cariboulabs/cariboulite_hw/doc/s-params/hfcn_from_cm.png

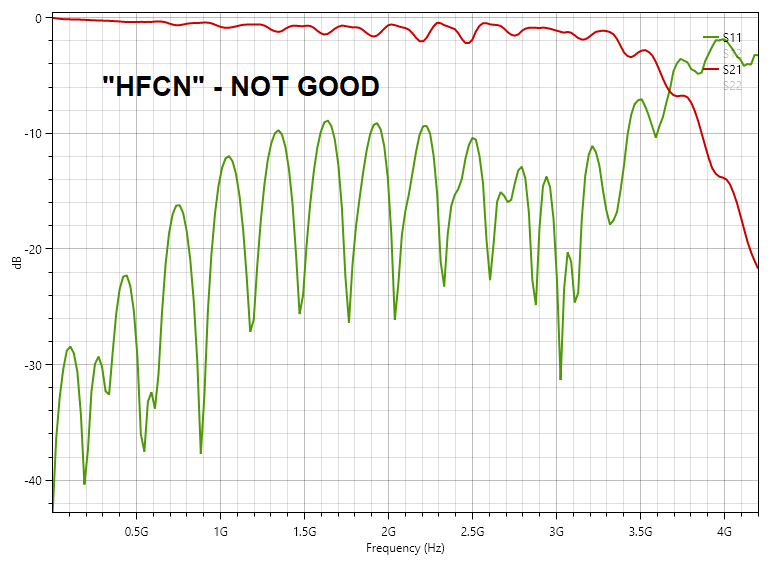
doc/s-params/hfcn_from_cm.png
