cariboulabs/cariboulite_hw/doc/s-params/hfcn_from_minicircuits.png

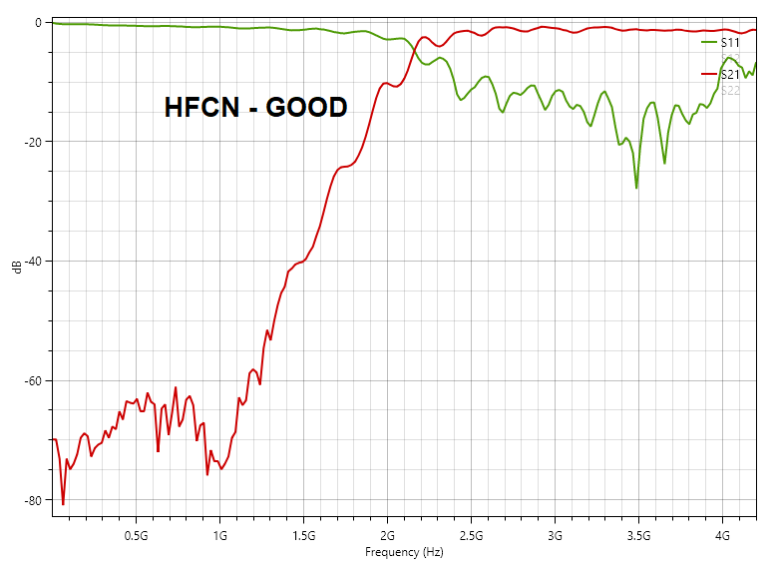
doc/s-params/hfcn_from_minicircuits.png
