cariboulabs/cariboulite_hw/doc/s-params/lineup.jpg

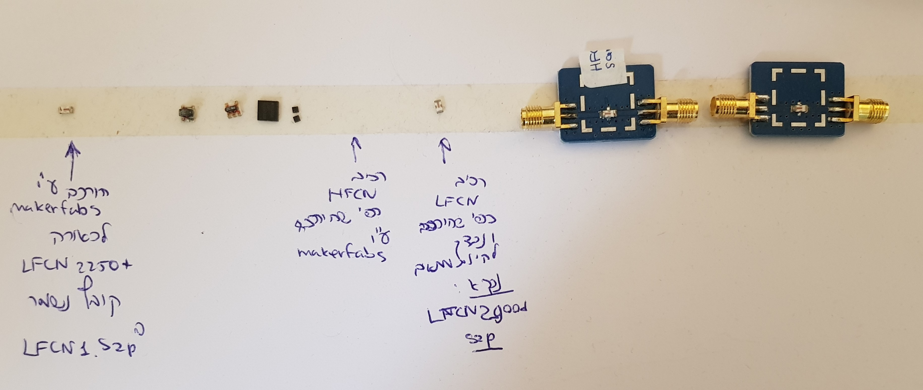
doc/s-params/lineup.jpg
