cariboulabs/cariboulite_hw/doc/screenshots/sdr_pp_fm_radio.png

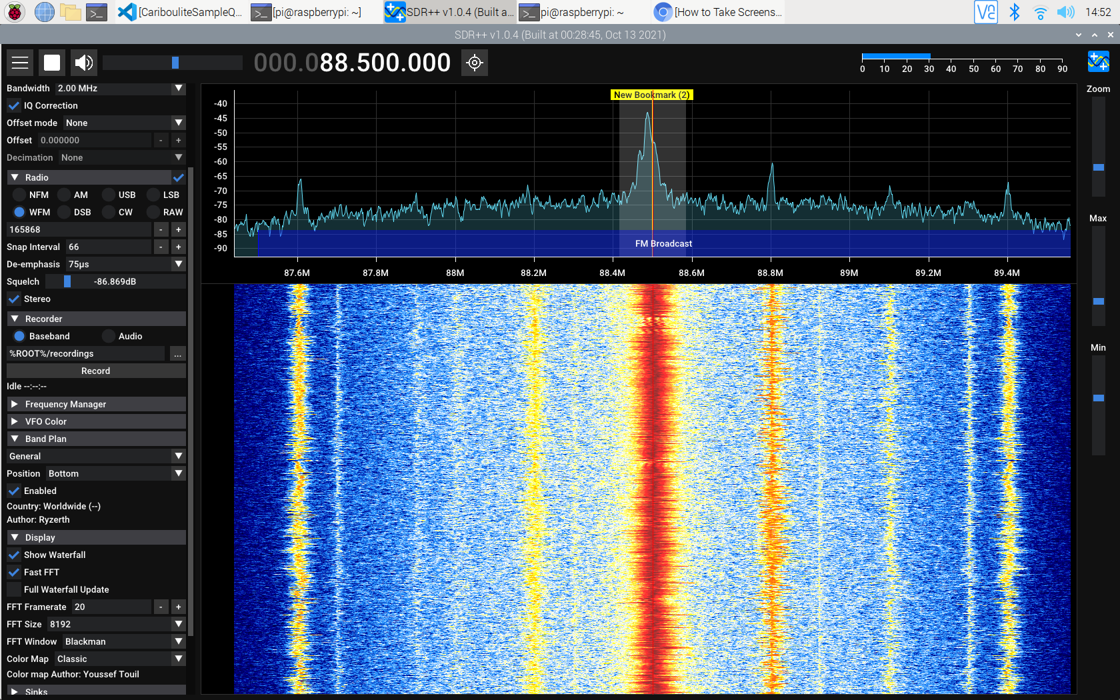
doc/screenshots/sdr_pp_fm_radio.png
