cariboulabs/cariboulite_hw/doc/screenshots/sdr_pp_ism.png

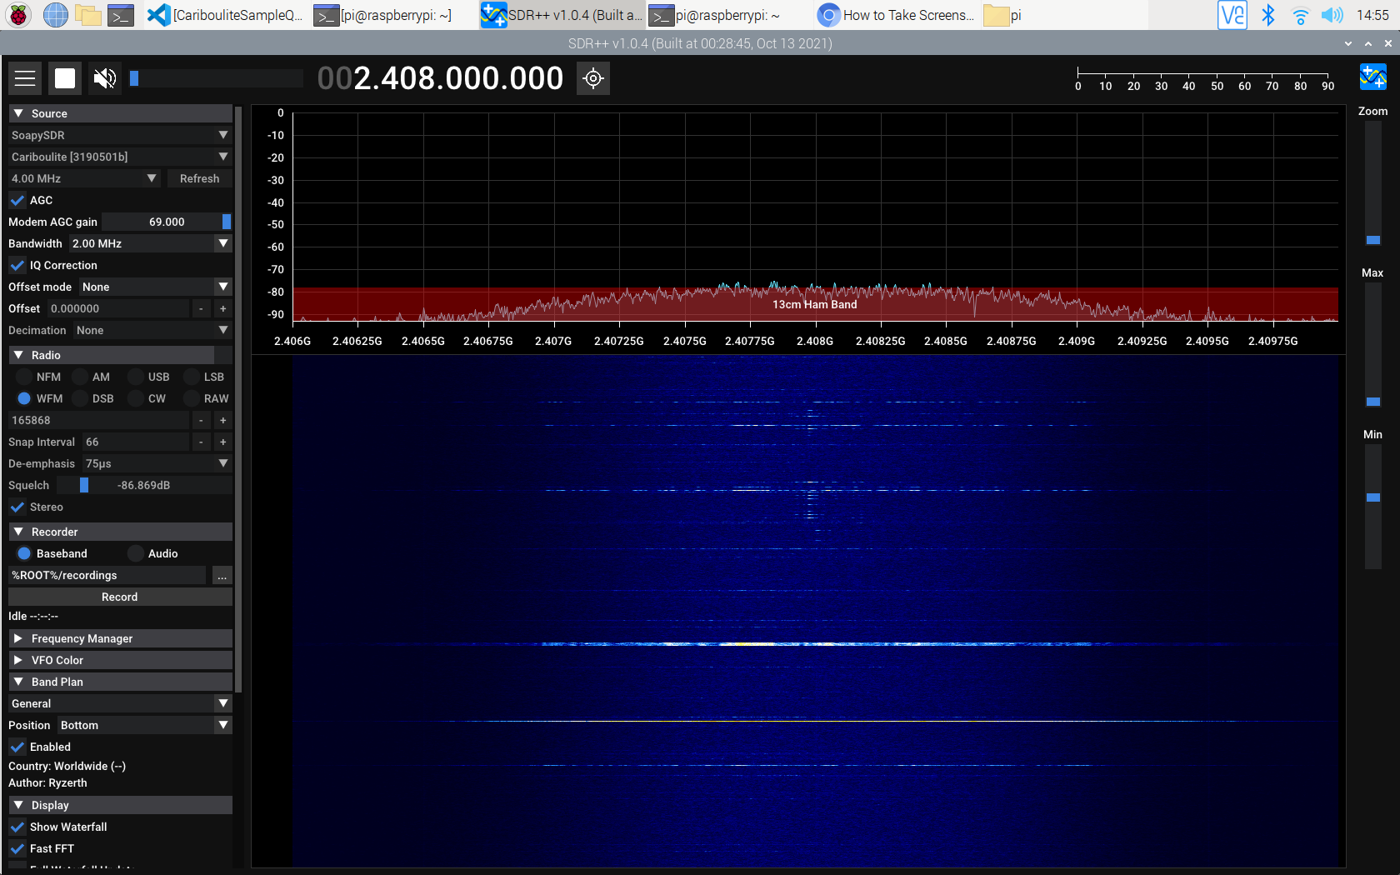
doc/screenshots/sdr_pp_ism.png
