cariboulabs/cariboulite_hw/doc/system/power_sketch.png

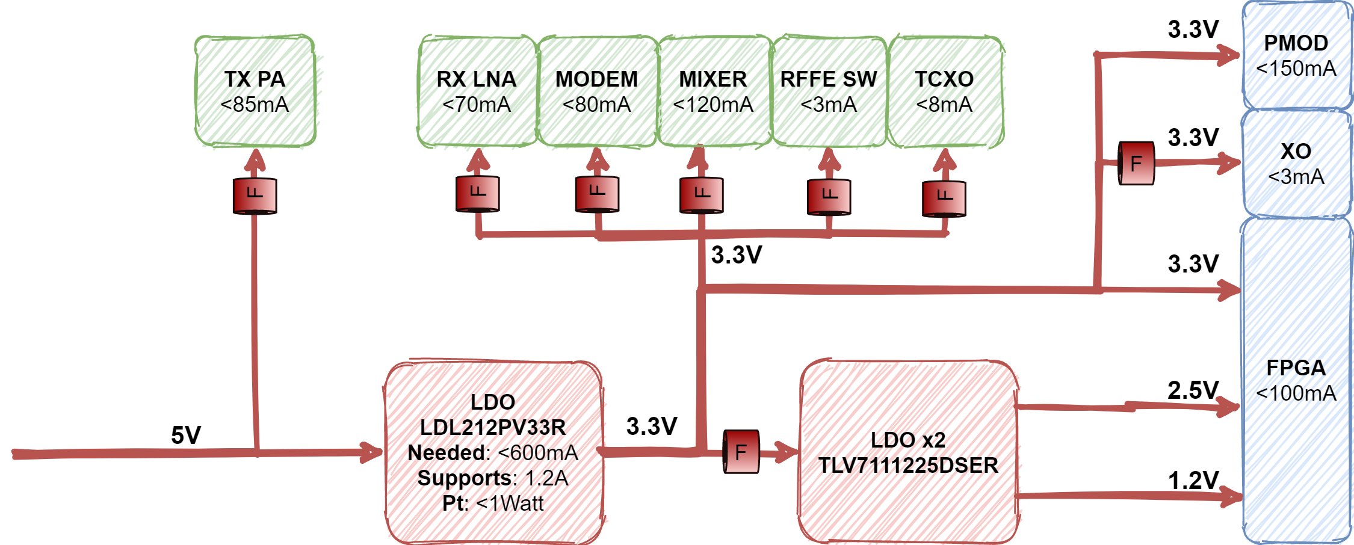
doc/system/power_sketch.png
