cariboulabs/cariboulite_hw/doc/system/ranges.png

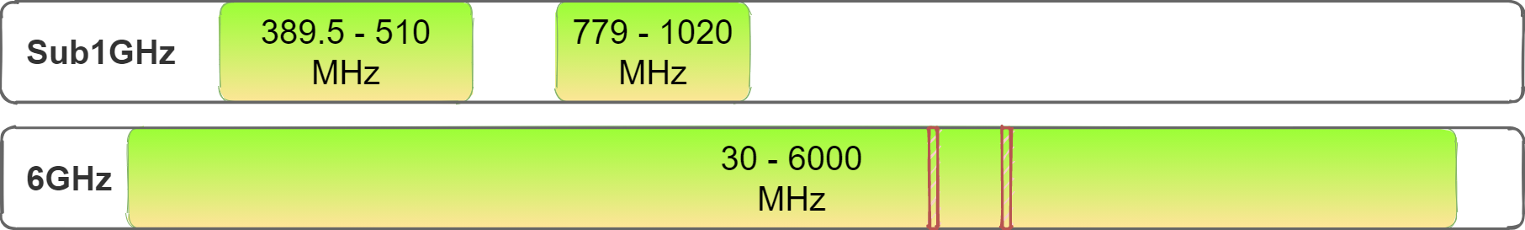
doc/system/ranges.png
