cariboulabs/cariboulite_hw/doc/system/ranges_ism.png

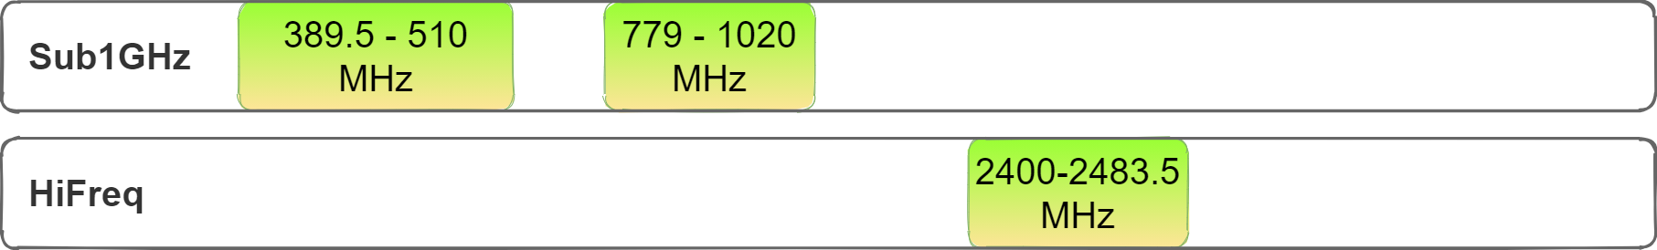
doc/system/ranges_ism.png
