cariboulabs/cariboulite_hw/doc/system/system_view_ism.png

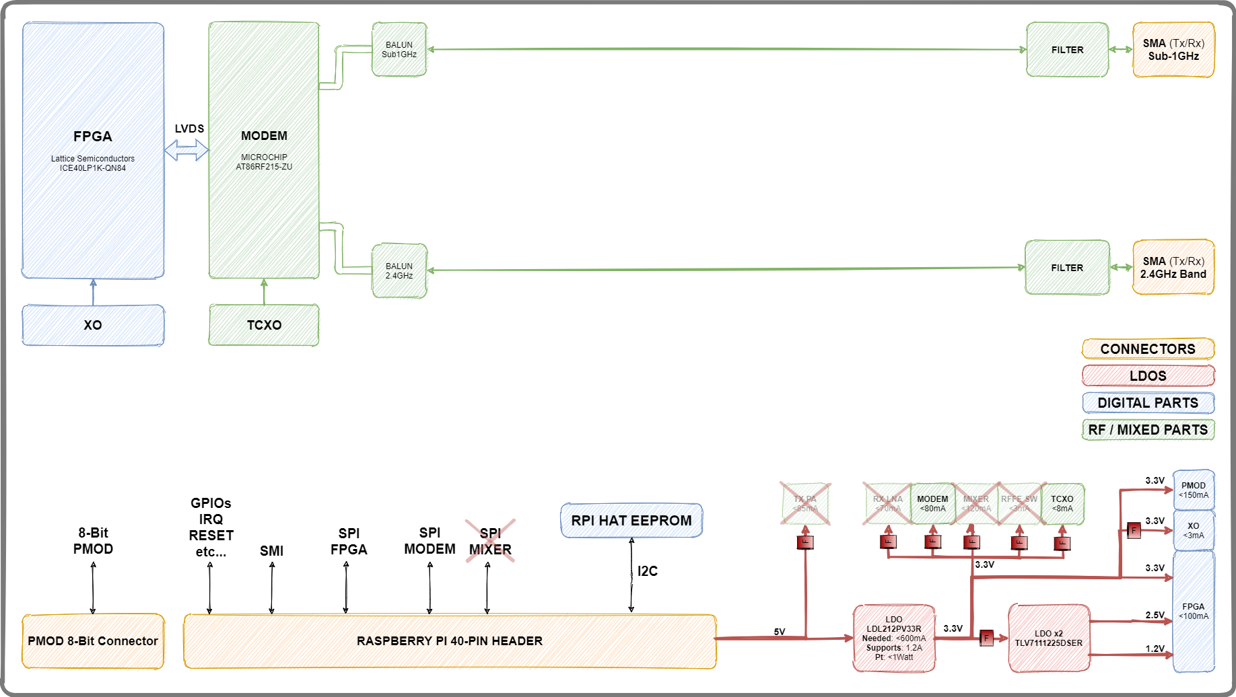
doc/system/system_view_ism.png
