cariboulabs/cariboulite_hw/hardware/rev2/pictures/BottomR2.8.png

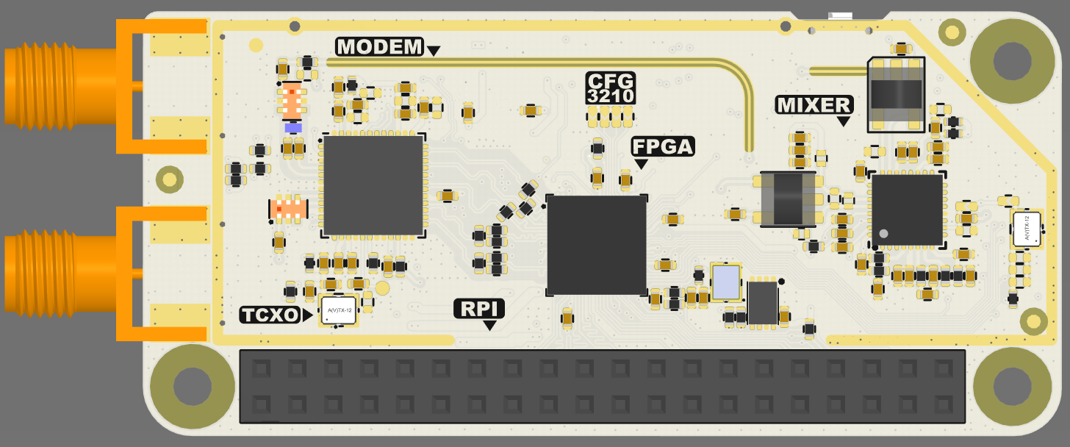
hardware/rev2/pictures/BottomR2.8.png
