cariboulabs/cariboulite_hw/hardware/rev2/pictures/cad_image_bw.png

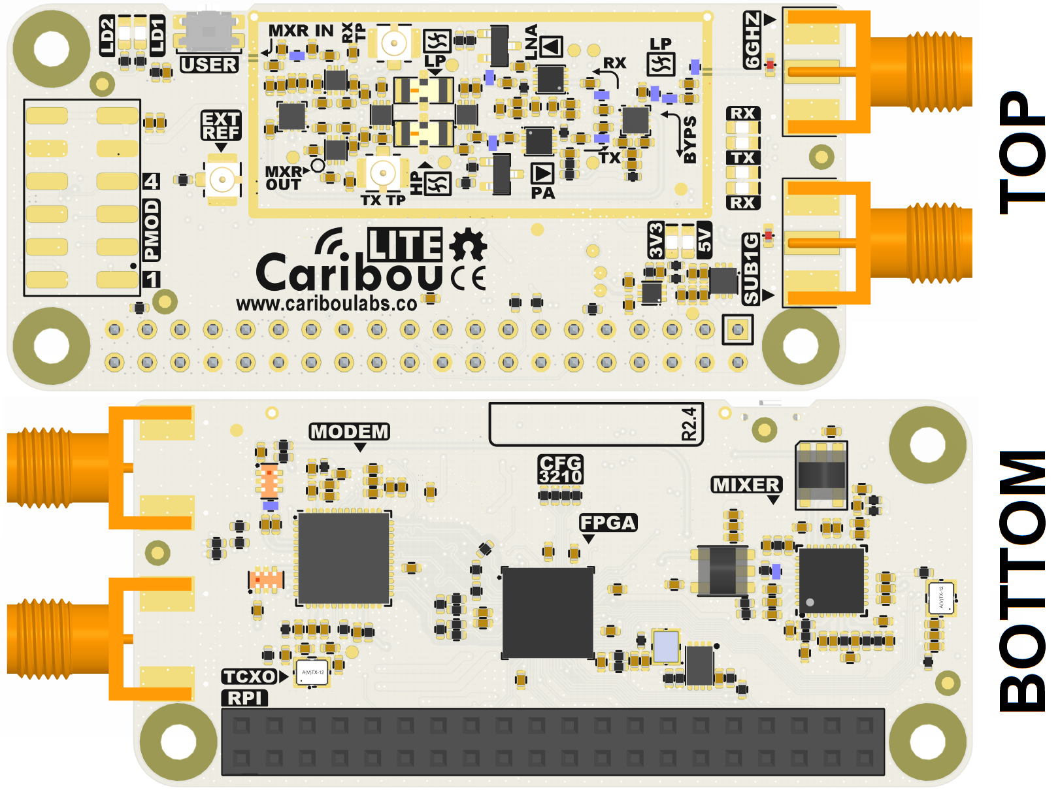
hardware/rev2/pictures/cad_image_bw.png
