cariboulabs/cariboulite_hw/hardware/rev2/pictures/DSC_0006.jpg

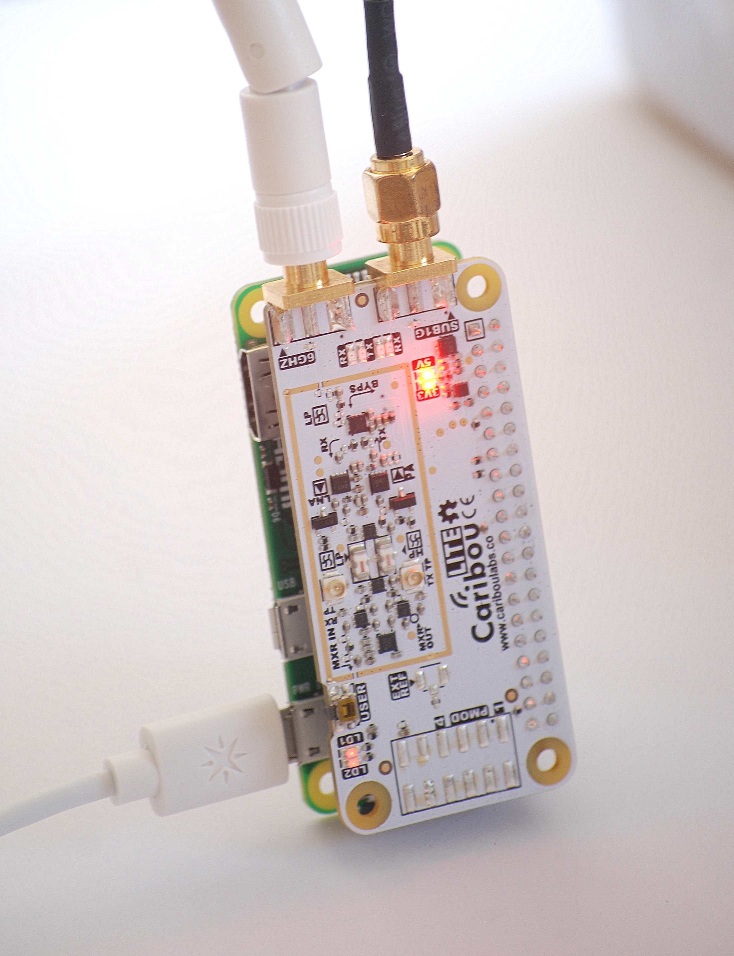
hardware/rev2/pictures/DSC_0006.jpg
