cariboulabs/cariboulite_hw/hardware/rev2/pictures/DSC_1108.jpg

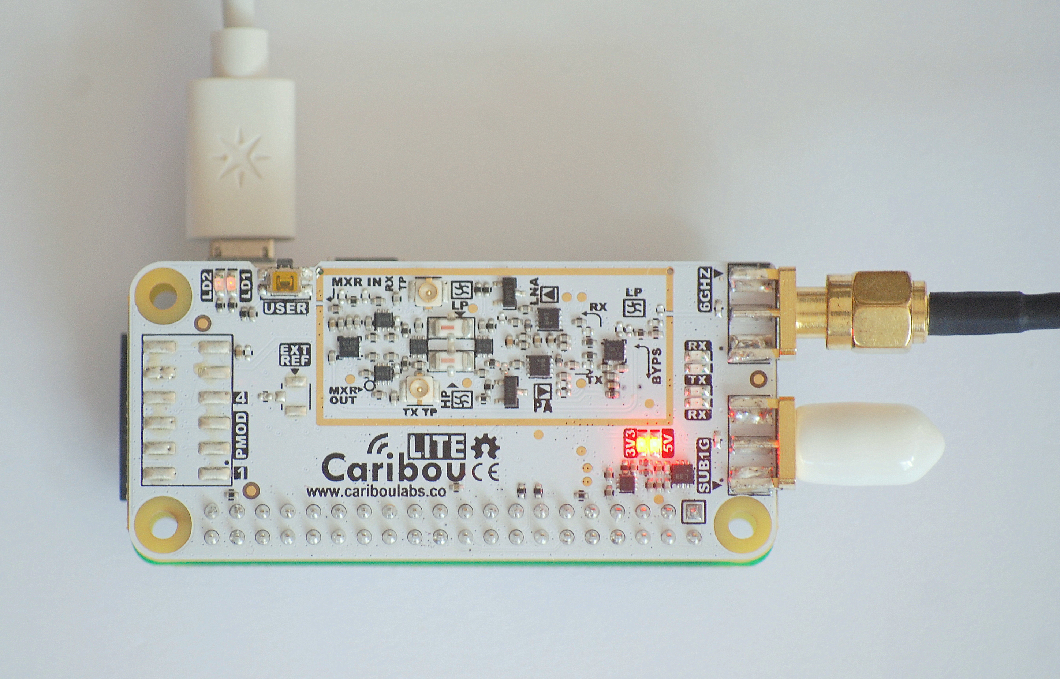
hardware/rev2/pictures/DSC_1108.jpg
