cariboulabs/cariboulite_hw/hardware/rev2/pictures/DSC_1117.jpg

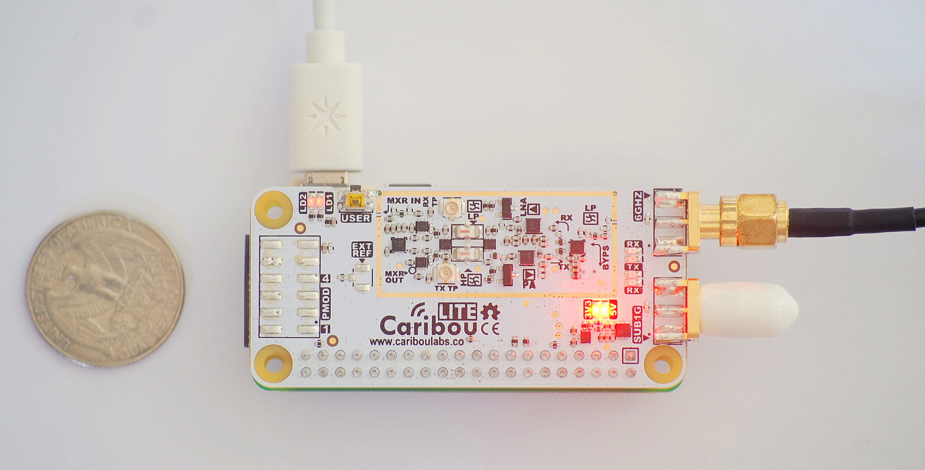
hardware/rev2/pictures/DSC_1117.jpg
