cariboulabs/cariboulite_hw/hardware/rev2/pictures/DSC_1134.jpg

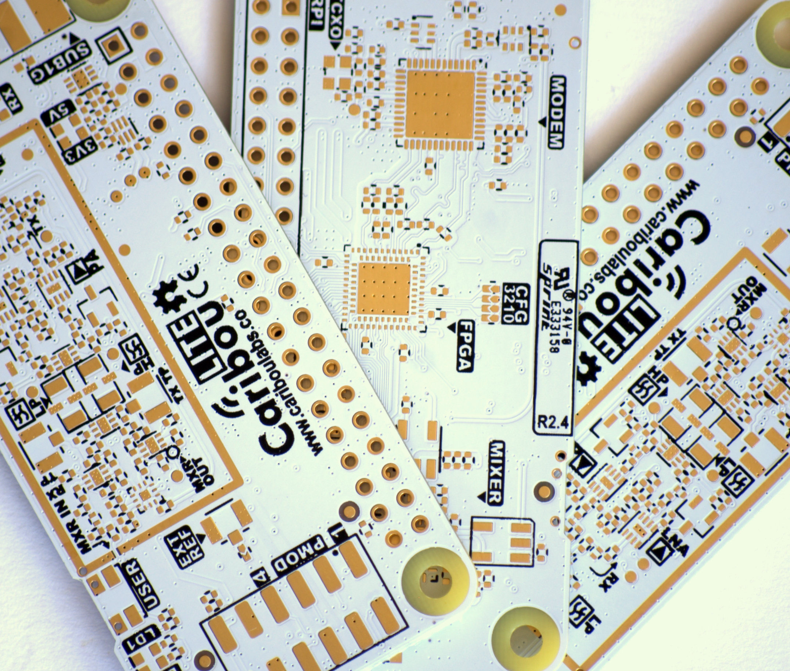
hardware/rev2/pictures/DSC_1134.jpg
