cariboulabs/cariboulite_hw/hardware/rev2/pictures/DSC_1136.jpg

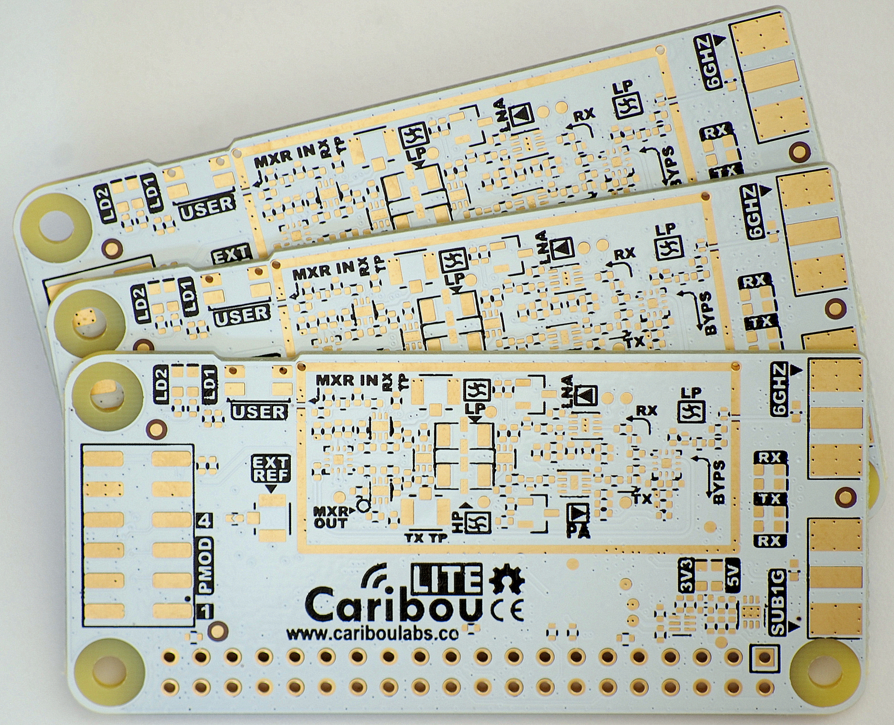
hardware/rev2/pictures/DSC_1136.jpg
