cariboulabs/cariboulite_hw/hardware/rev2/pictures/DSC_1145.jpg

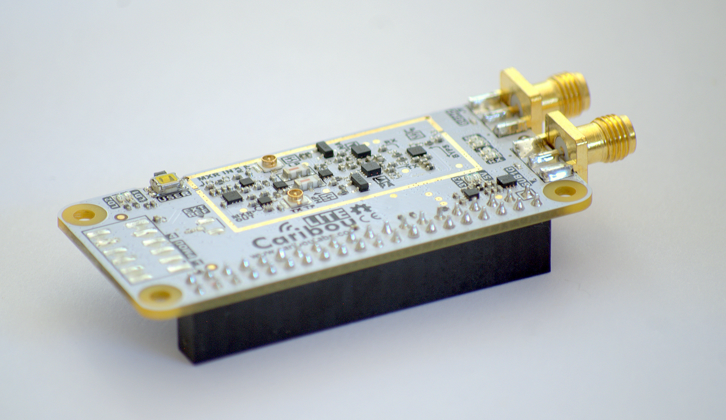
hardware/rev2/pictures/DSC_1145.jpg
