cariboulabs/cariboulite_hw/hardware/rev2/pictures/DSC_1146.jpg

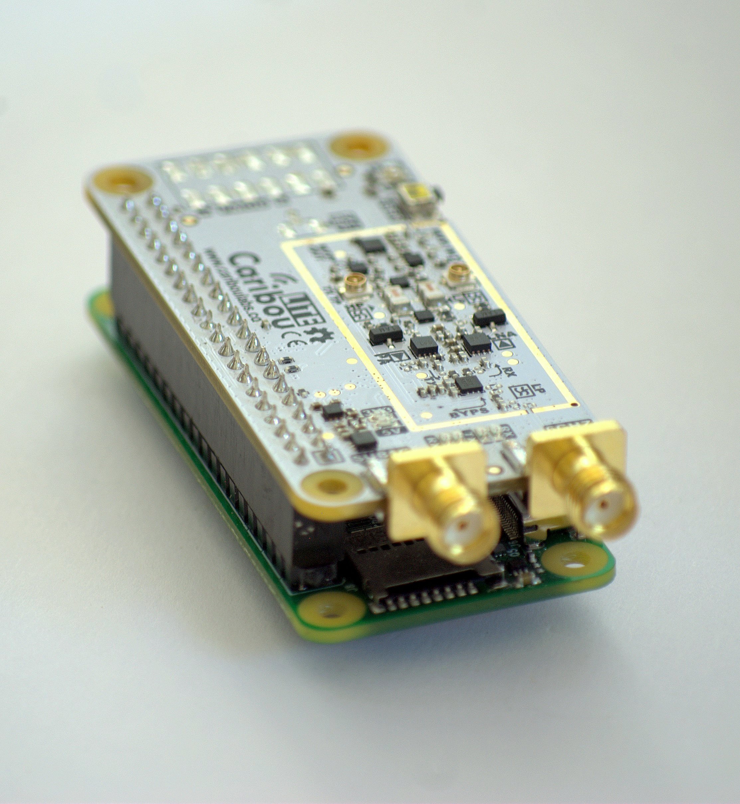
hardware/rev2/pictures/DSC_1146.jpg
