cariboulabs/cariboulite_hw/hardware/rev2/pictures/DSC_1149.jpg

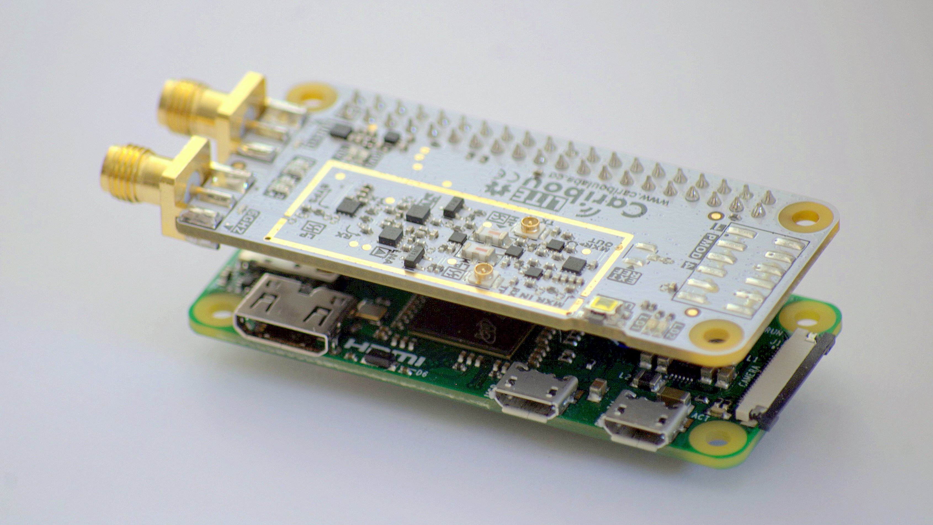
hardware/rev2/pictures/DSC_1149.jpg
