cariboulabs/cariboulite_hw/hardware/rev2/pictures/DSC_1152.jpg

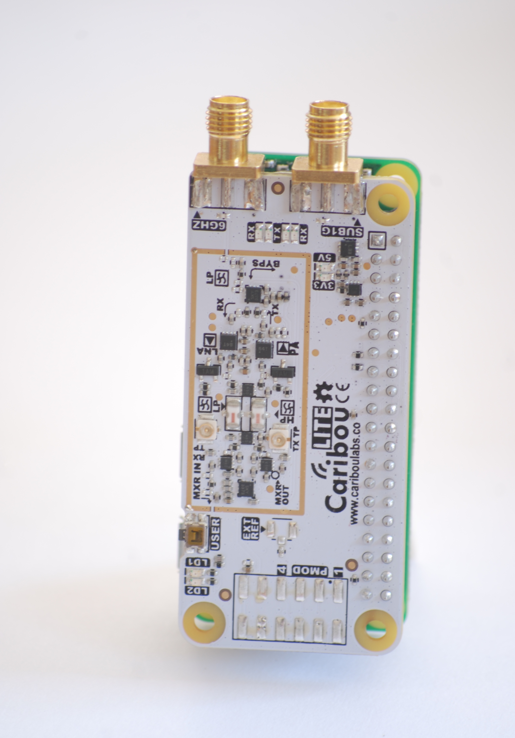
hardware/rev2/pictures/DSC_1152.jpg
