cariboulabs/cariboulite_hw/hardware/rev2/pictures/DSC_11441.jpg

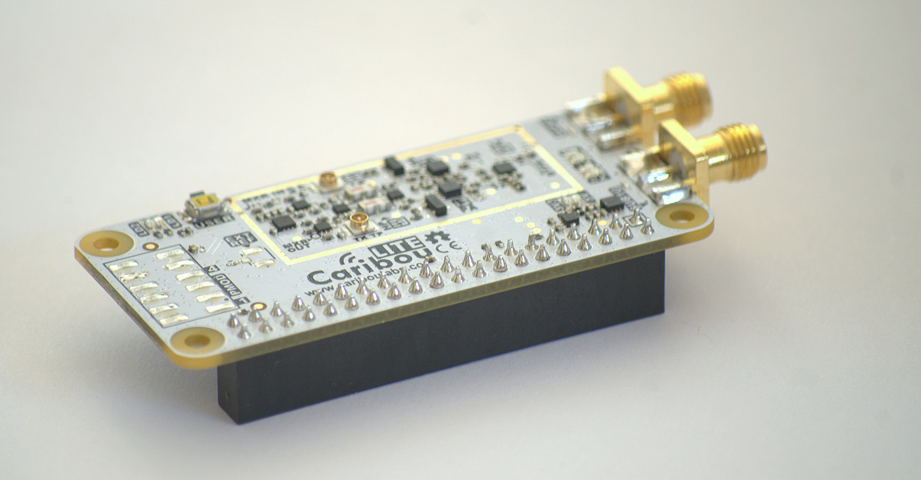
hardware/rev2/pictures/DSC_11441.jpg
