cariboulabs/cariboulite_hw/hardware/rev2/pictures/focus_gp_leds.png

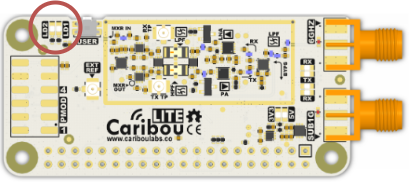
hardware/rev2/pictures/focus_gp_leds.png
