cariboulabs/cariboulite_hw/hardware/rev2/pictures/Rev2.5/colors_black.png

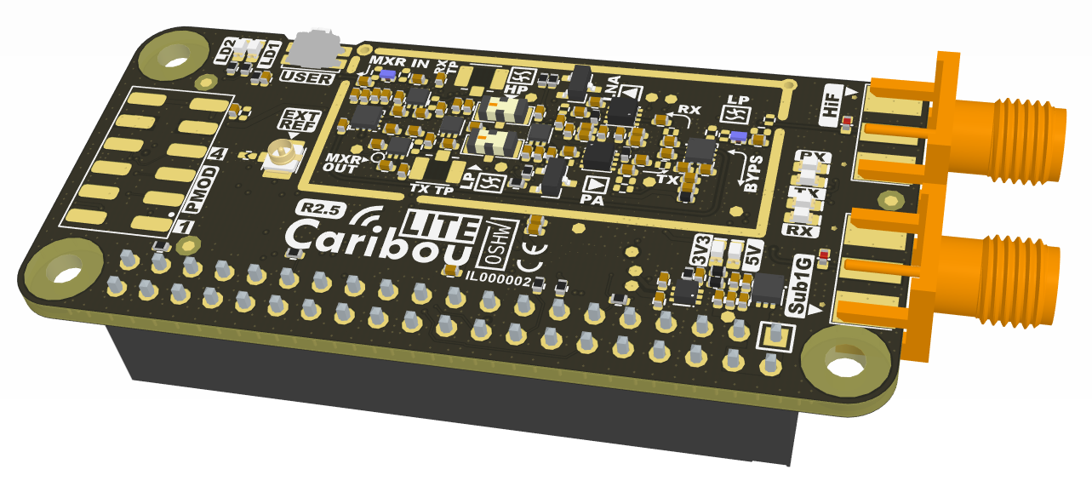
hardware/rev2/pictures/Rev2.5/colors_black.png
