cariboulabs/cariboulite_hw/hardware/rev2/pictures/Rev2.5/colors_red.png

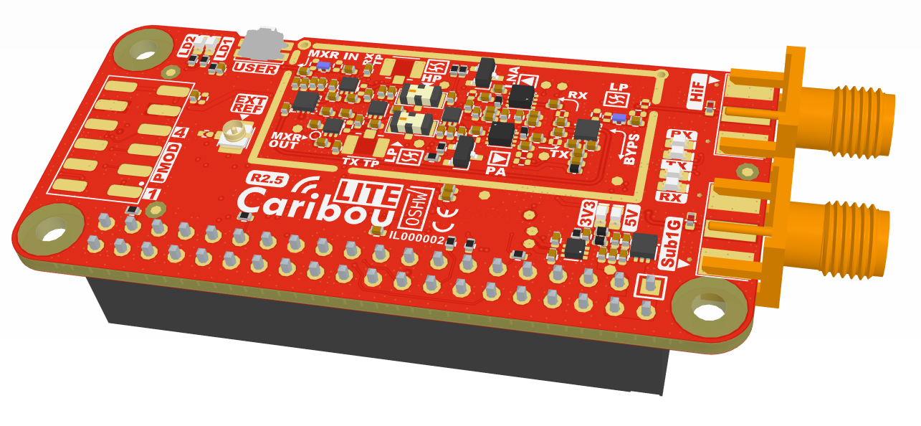
hardware/rev2/pictures/Rev2.5/colors_red.png
