cariboulabs/cariboulite_hw/hardware/rev2/pictures/Rev2.5/perspective.png

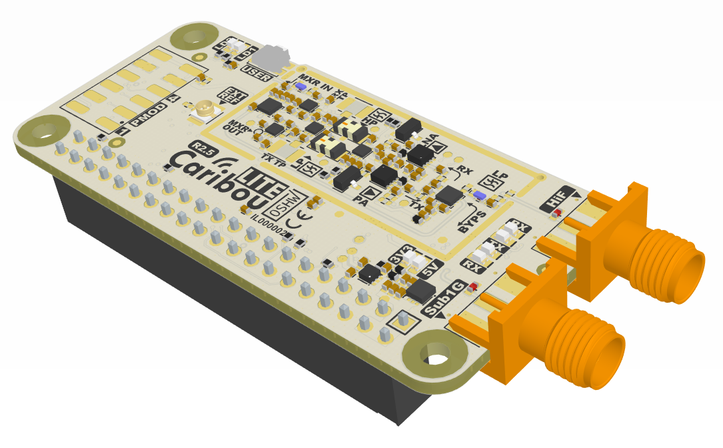
hardware/rev2/pictures/Rev2.5/perspective.png
