cariboulabs/cariboulite_hw/hardware/rev2/pictures/TopR2.8.png

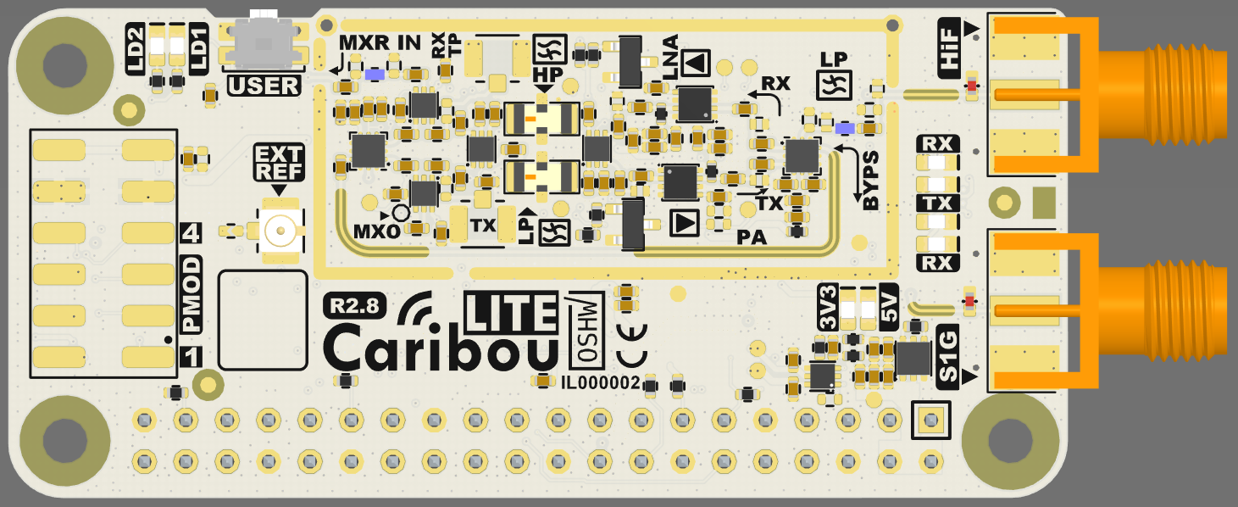
hardware/rev2/pictures/TopR2.8.png
