cariboulabs/cariboulite_hw/doc/system/instruction_eeprom_wp.png

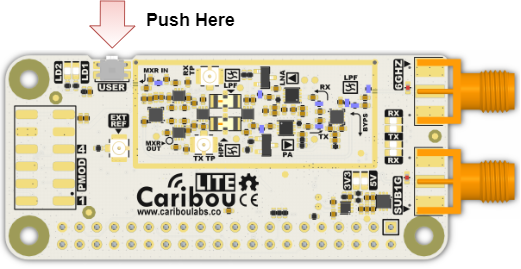
doc/system/instruction_eeprom_wp.png
